vkshardware/GPS_Speedometer_G2.2/ABS/01.jpg

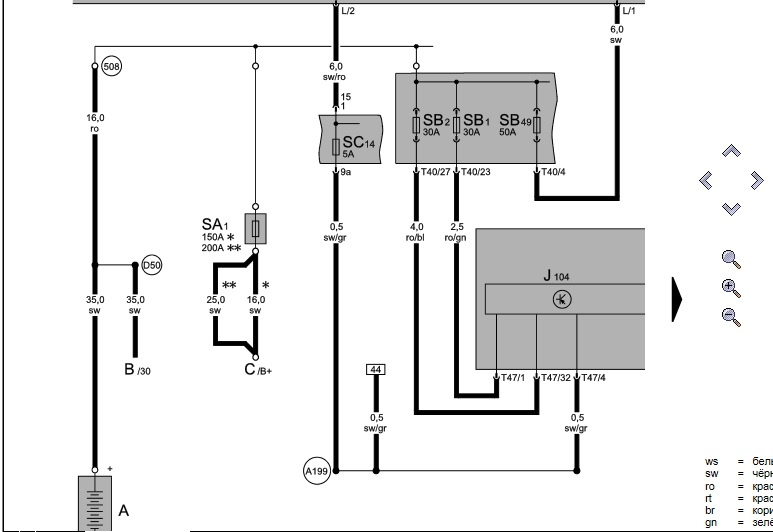
ABS/01.jpg
