vkshardware/GPS_Speedometer_G2.2/ABS/02.jpg

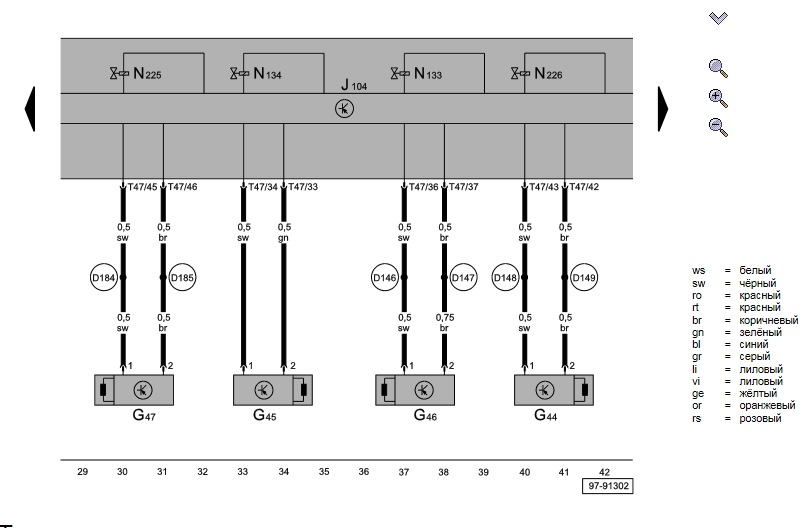
ABS/02.jpg
