vkshardware/GPS_Speedometer_G2.2/ABS/03.jpg

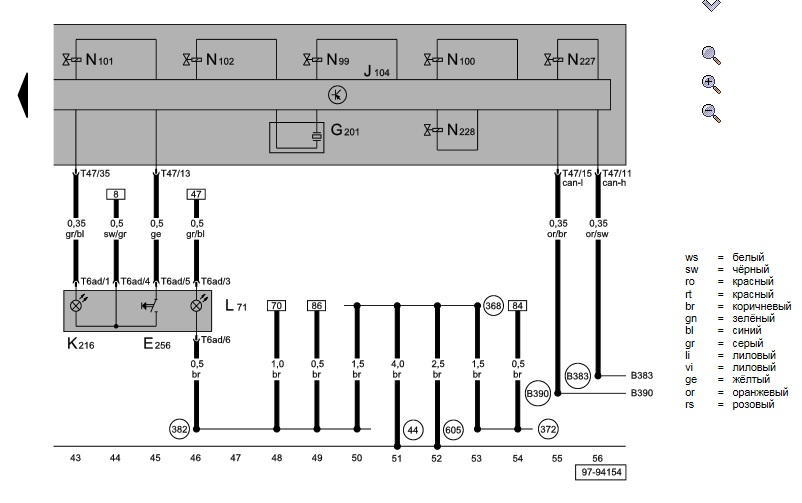
ABS/03.jpg
