vkshardware/GPS_Speedometer_G2.2/photos_and_schemes/01___.png

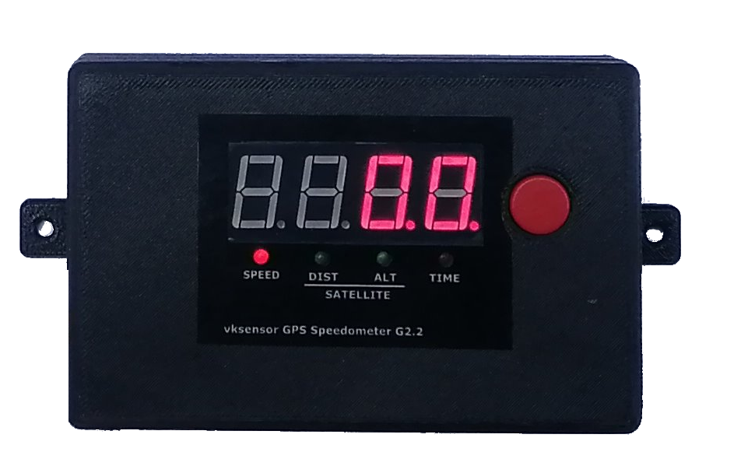
photos_and_schemes/01___.png
