vkshardware/GPS_Speedometer_G2.2/photos_and_schemes/02_.jpg

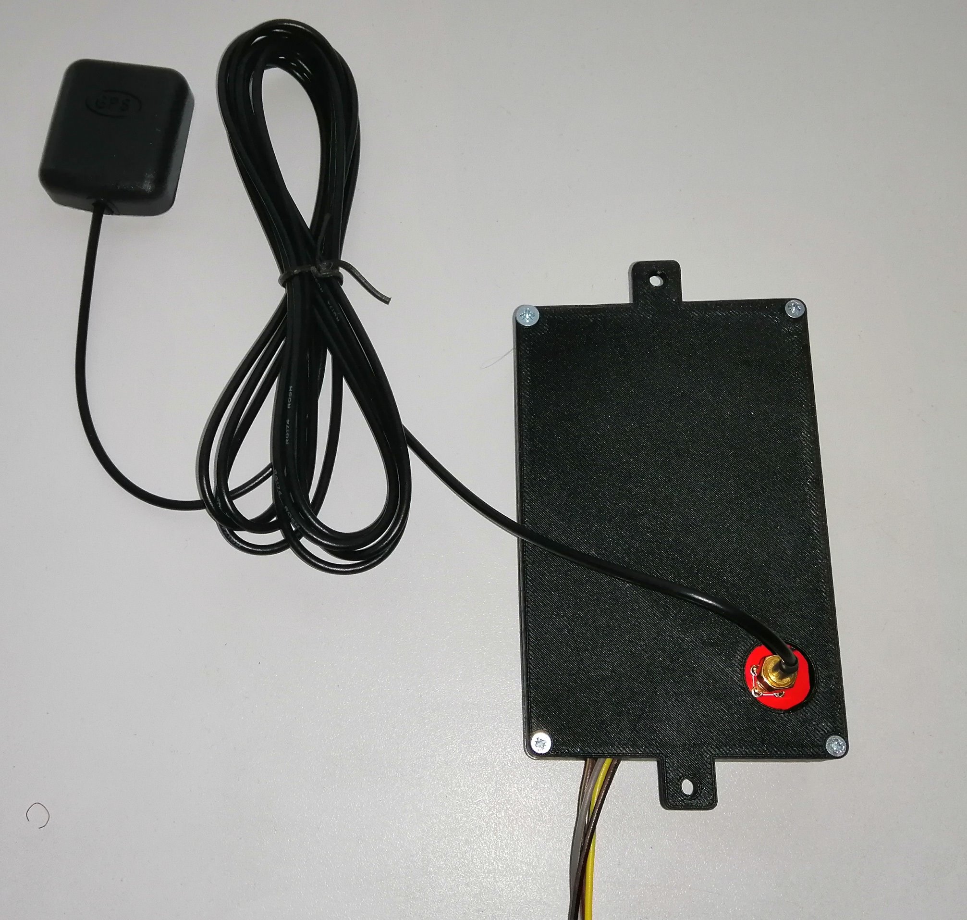
photos_and_schemes/02_.jpg
