vkshardware/GPS_Speedometer_G2.2/photos_and_schemes/03.jpg

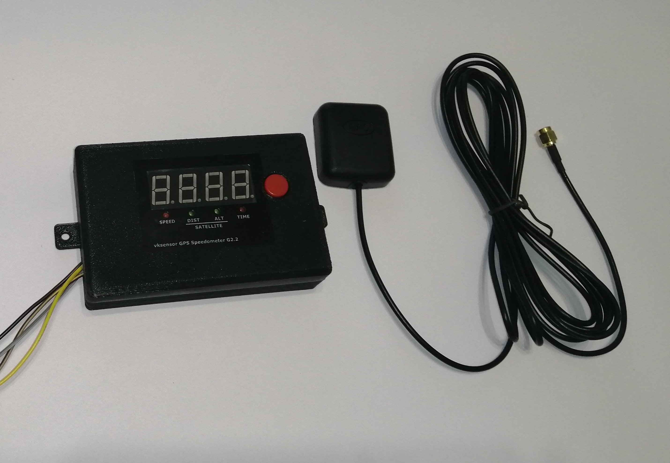
photos_and_schemes/03.jpg
