vkshardware/GPS_Speedometer_G2.2/photos_and_schemes/03__.jpg

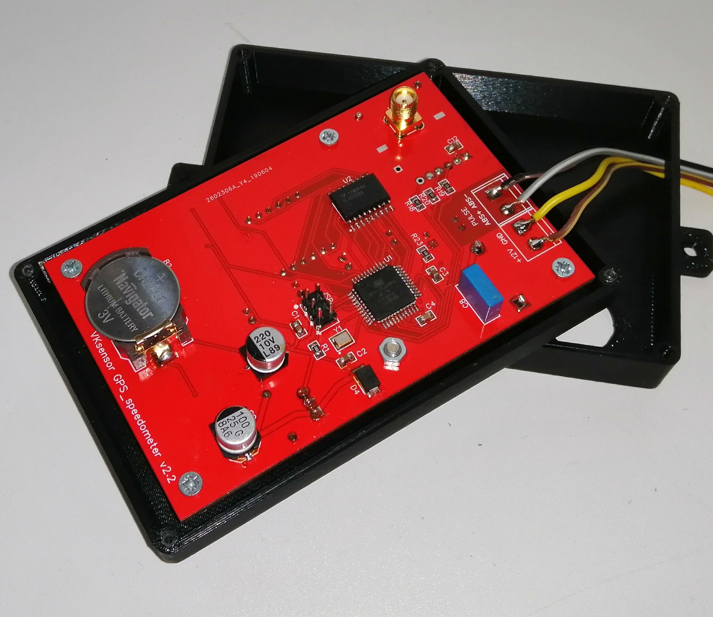
photos_and_schemes/03__.jpg
