vkshardware/GPS_Speedometer_G2.2/photos_and_schemes/12_1.jpg

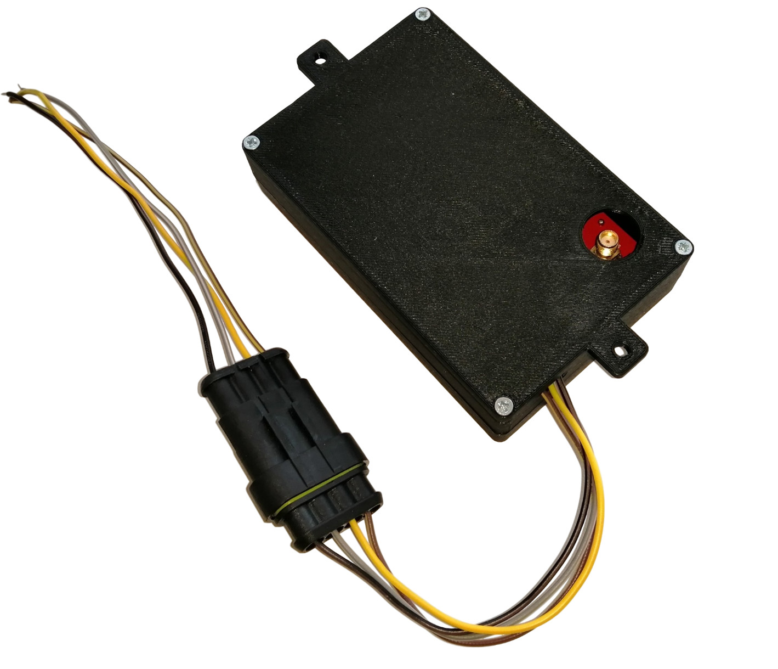
photos_and_schemes/12_1.jpg
