vkshardware/GPS_Speedometer_G2.2/photos_and_schemes/out.png

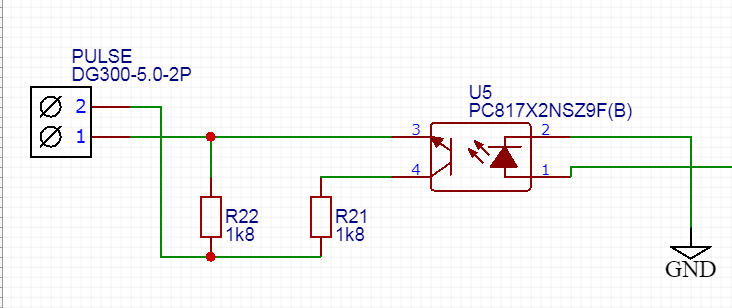
photos_and_schemes/out.png
