vkshardware/GPS_Speedometer_G2.2/photos_and_schemes/podkl02_eng.png.png

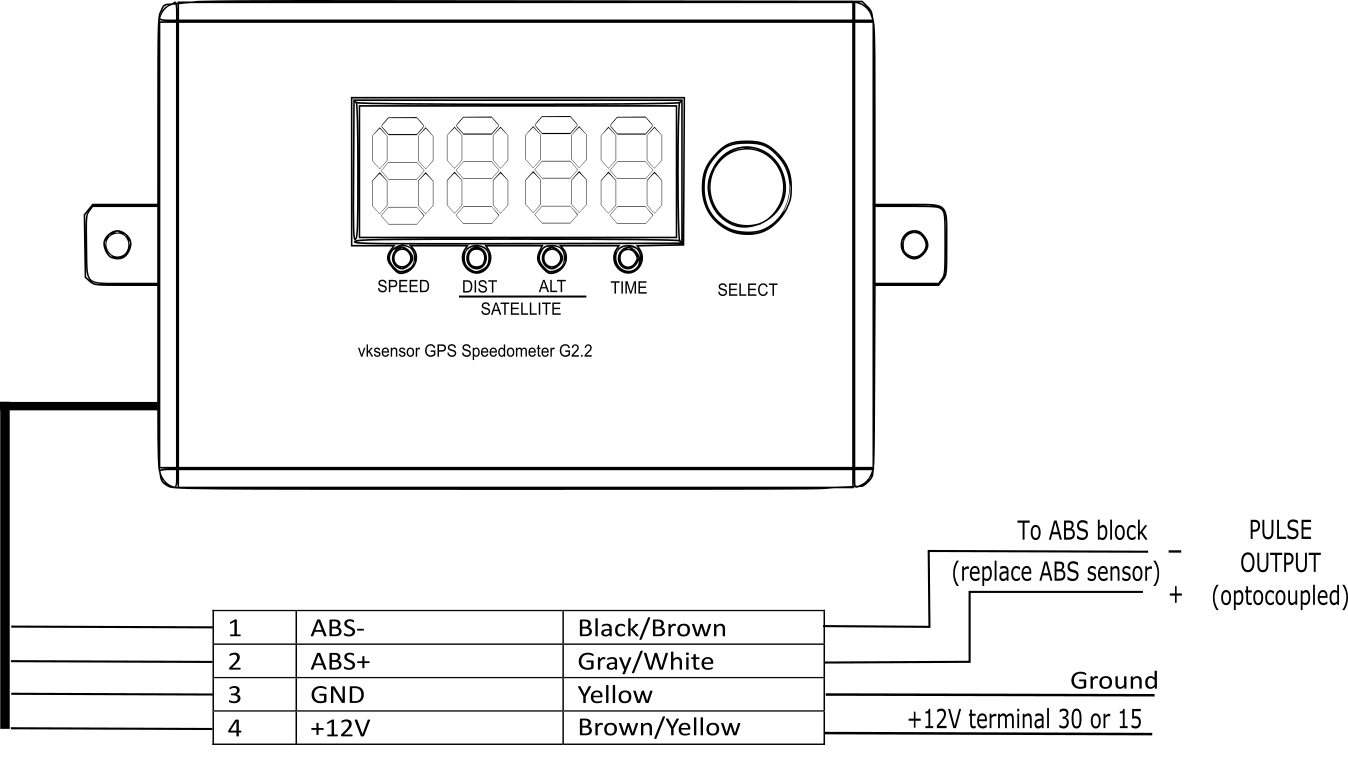
photos_and_schemes/podkl02_eng.png.png
